bbcmicrobit/prototype/device/historical/20140923_MiniMicro/MiniMicro_PCB_3DSnapshot.png

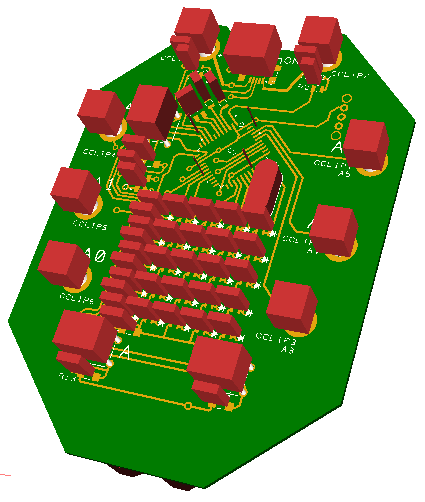
device/historical/20140923_MiniMicro/MiniMicro_PCB_3DSnapshot.png
