bbcmicrobit/prototype/dal/003/spark_font.h

#
# Copyright 2016 British Broadcasting Corporation and Contributors(1)
#
# (1) Contributors are listed in the AUTHORS file (please extend AUTHORS,
#     not this header)
#
# Licensed under the Apache License, Version 2.0 (the "License");
# you may not use this file except in compliance with the License.
# You may obtain a copy of the License at
#
#     http://www.apache.org/licenses/LICENSE-2.0
#
# Unless required by applicable law or agreed to in writing, software
# distributed under the License is distributed on an "AS IS" BASIS,
# WITHOUT WARRANTIES OR CONDITIONS OF ANY KIND, either express or implied.
# See the License for the specific language governing permissions and
# limitations under the License.
#

/*                                                                       */
/* DO NOT EDIT THIS (autogenerated) FILE                                 */
/* To make changes to the font, edit py2cc/gen_font_4x5.py instead       */
/*                                                                       */
   const unsigned char font[95][6] = {
                      {32, 0b0000, 0b0000, 0b0000, 0b0000, 0b0000},
                      {33, 0b0100, 0b0100, 0b0100, 0b0000, 0b0100},
                      {34, 0b1010, 0b1010, 0b0000, 0b0000, 0b0000},
                      {35, 0b1010, 0b1111, 0b1010, 0b1111, 0b1010},
                      {36, 0b0110, 0b1101, 0b0110, 0b1011, 0b0110},
                      {37, 0b1001, 0b0010, 0b0100, 0b1001, 0b0000},
                      {38, 0b0110, 0b0100, 0b1001, 0b0110, 0b0000},
                      {39, 0b1000, 0b1000, 0b0000, 0b0000, 0b0000},
                      {40, 0b0001, 0b0010, 0b0010, 0b0010, 0b0001},
                      {41, 0b1000, 0b0100, 0b0100, 0b0100, 0b1000},
                      {42, 0b0000, 0b1010, 0b0100, 0b1010, 0b0000},
                      {43, 0b0000, 0b0100, 0b1110, 0b0100, 0b0000},
                      {44, 0b0000, 0b0000, 0b0000, 0b0100, 0b0100},
                      {45, 0b0000, 0b0000, 0b1110, 0b0000, 0b0000},
                      {46, 0b0000, 0b0000, 0b0000, 0b0100, 0b0000},
                      {47, 0b0010, 0b0010, 0b0100, 0b1000, 0b1000},
                      {48, 0b0100, 0b1010, 0b1010, 0b1010, 0b0100},
                      {49, 0b0100, 0b1100, 0b0100, 0b0100, 0b0100},
                      {50, 0b1110, 0b0001, 0b0110, 0b1000, 0b1111},
                      {51, 0b1111, 0b0001, 0b0010, 0b1001, 0b0110},
                      {52, 0b1000, 0b1010, 0b1010, 0b1111, 0b0010},
                      {53, 0b1111, 0b1000, 0b0110, 0b0001, 0b1110},
                      {54, 0b0111, 0b1000, 0b1110, 0b1001, 0b1110},
                      {55, 0b1111, 0b0001, 0b0010, 0b0100, 0b0100},
                      {56, 0b0110, 0b1001, 0b0110, 0b1001, 0b0110},
                      {57, 0b0111, 0b1001, 0b0111, 0b0001, 0b0001},
                      {58, 0b0000, 0b0100, 0b0000, 0b0100, 0b0000},
                      {59, 0b0000, 0b0100, 0b0000, 0b0100, 0b0100},
                      {60, 0b0001, 0b0010, 0b0100, 0b0010, 0b0001},
                      {61, 0b0000, 0b1110, 0b0000, 0b1110, 0b0000},
                      {62, 0b0100, 0b0010, 0b0001, 0b0010, 0b0100},
                      {63, 0b0110, 0b1001, 0b0010, 0b0000, 0b0110},
                      {64, 0b0111, 0b1011, 0b1011, 0b1000, 0b0110},
                      {65, 0b0110, 0b1001, 0b1001, 0b1111, 0b1001},
                      {66, 0b1110, 0b1001, 0b1110, 0b1001, 0b1110},
                      {67, 0b0111, 0b1000, 0b1000, 0b1000, 0b0111},
                      {68, 0b1110, 0b1001, 0b1001, 0b1001, 0b1110},
                      {69, 0b1111, 0b1000, 0b1110, 0b1000, 0b1111},
                      {70, 0b1111, 0b1000, 0b1110, 0b1000, 0b1000},
                      {71, 0b0111, 0b1000, 0b1011, 0b1001, 0b0111},
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
                     };
